cracked-machine/STM32MP1_TestBoard_RevB/STM32MP1_TestBoard_RevB/DDR.sch

## KiCad design STM32MP1_TestBoard_RevB/DDR.sch (2021-04-06)

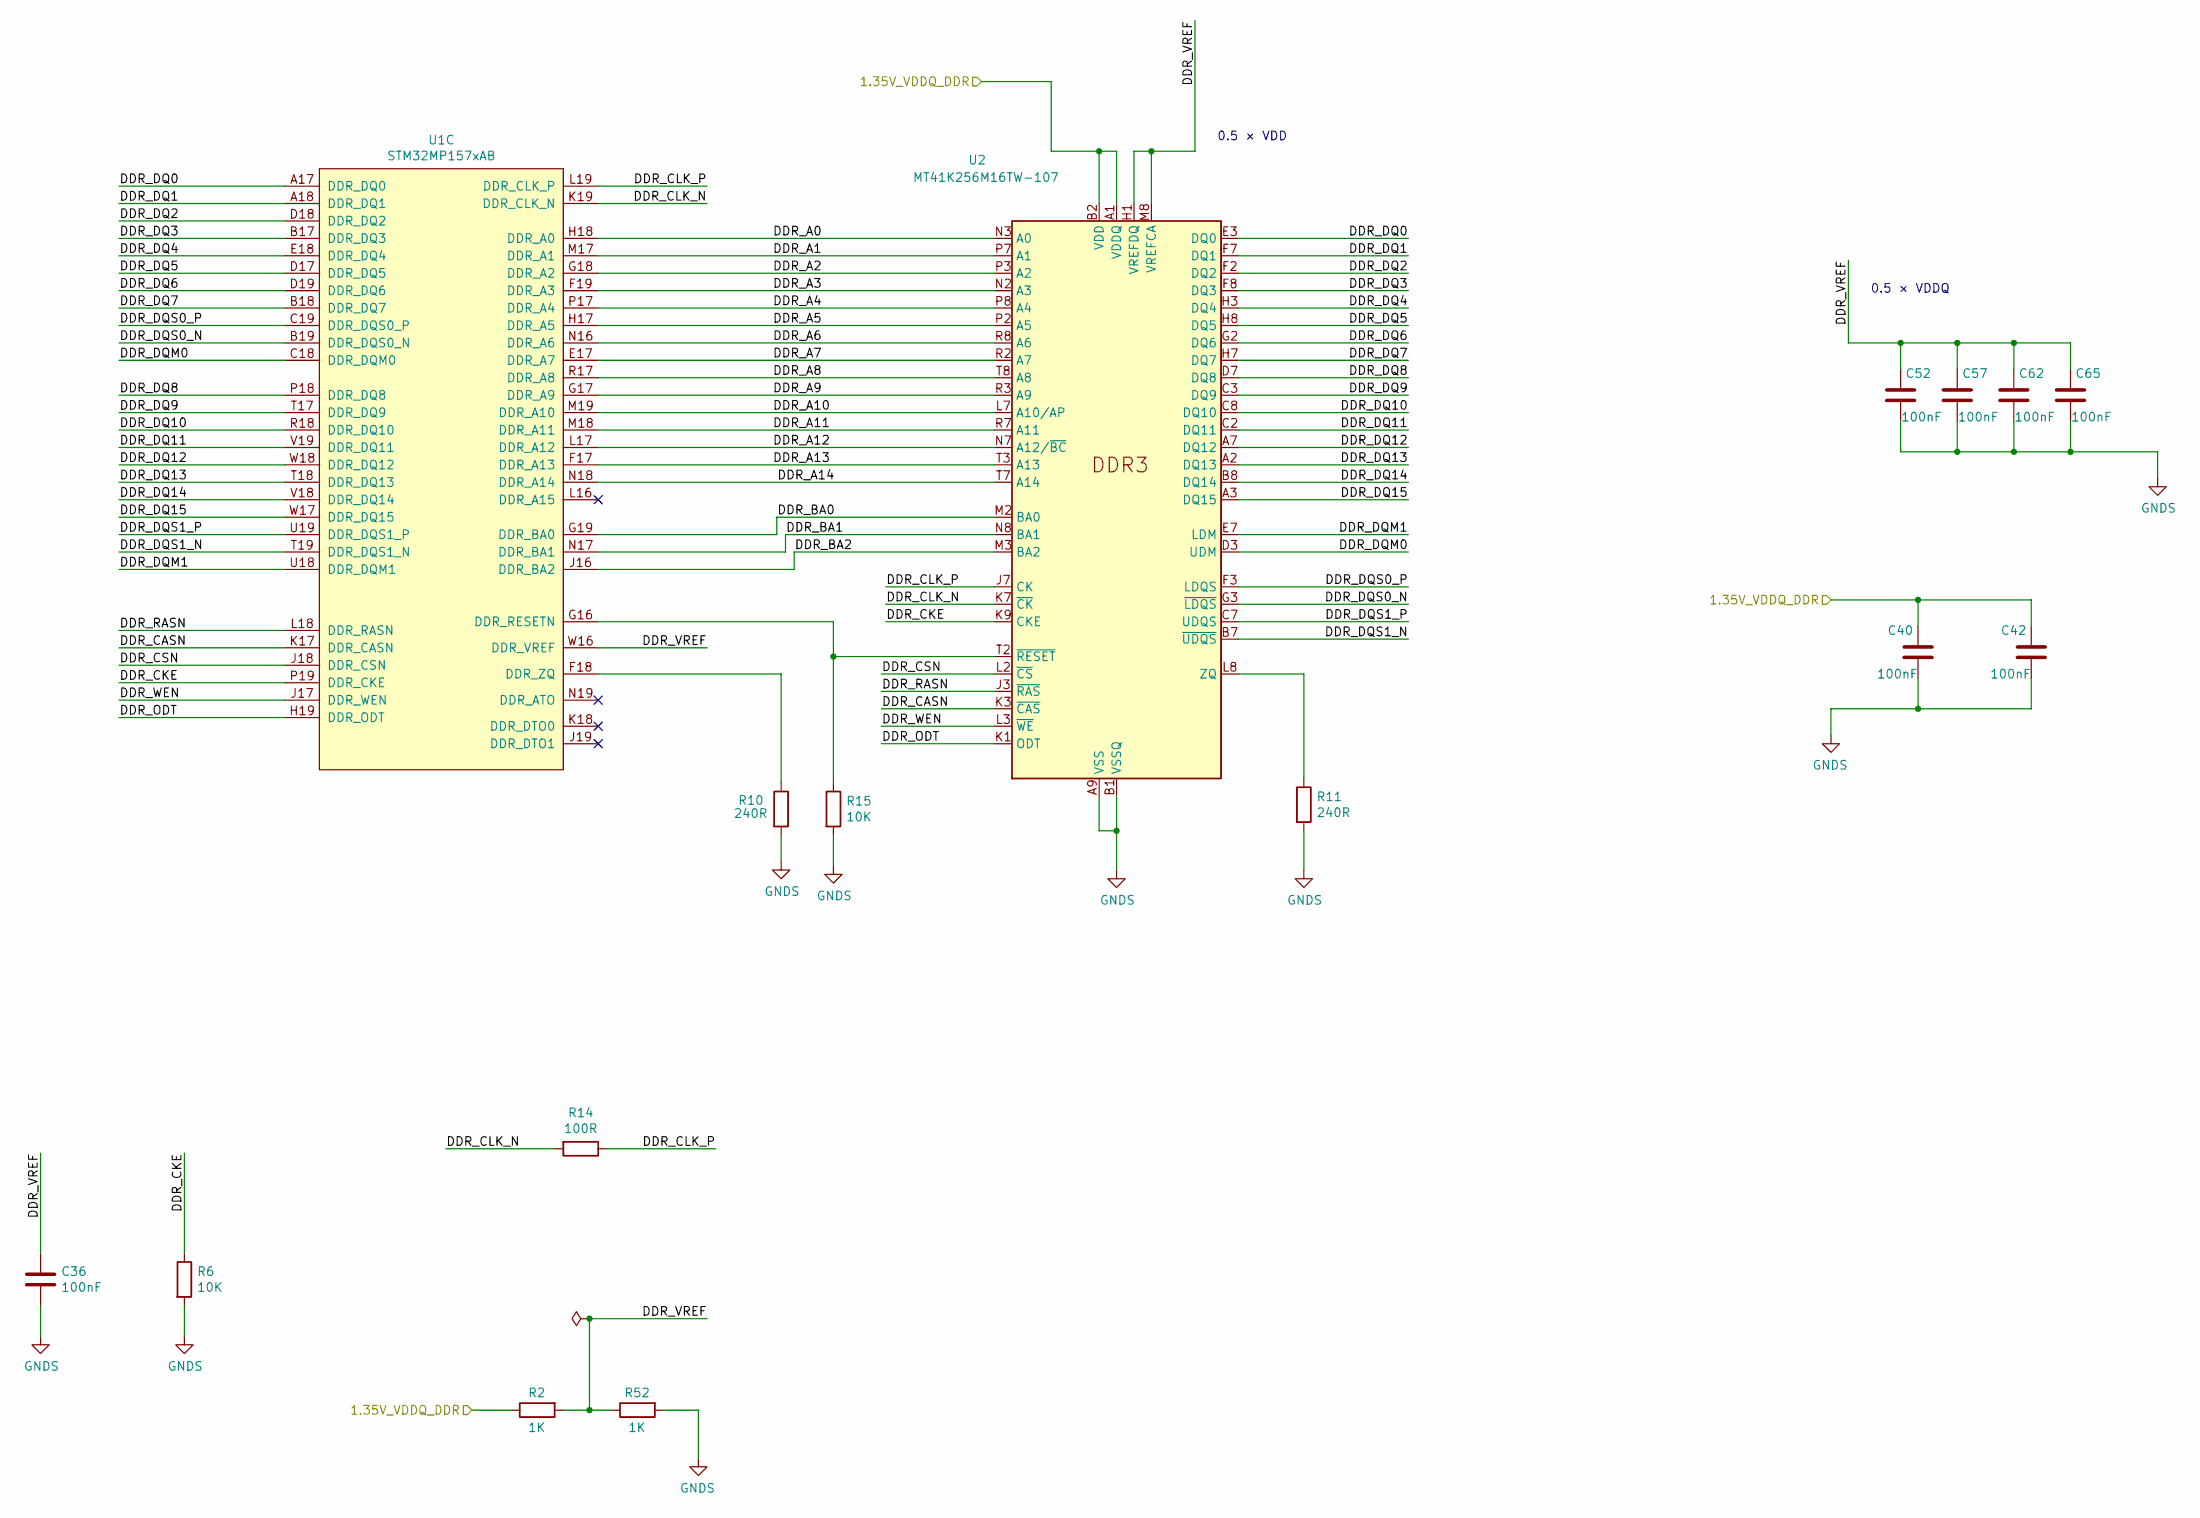
[picture p23: schematic DDR.sch]

Parts:
C36, C40, C42, C52, C57, C62, C65: 100nF; C_0402_1005Metric_Pad0.74x0.62mm_HandSolder; LCSC C1525
R2, R52: 1K; R_0402_1005Metric_Pad0.72x0.64mm_HandSolder; LCSC C11702
R6, R15: 10K; R_0402_1005Metric_Pad0.72x0.64mm_HandSolder; LCSC C25744
R10, R11: 240R; R_0402_1005Metric_Pad0.72x0.64mm_HandSolder
R14: 100R; R_0402_1005Metric_Pad0.72x0.64mm_HandSolder; LCSC C25076
U1: STM32MP157xAB; BGA-354_19x19_16.0x16.0mm
U2: MT41K256M16TW-107; BGA-96_9.0x13.0mm_Layout2x3x16_P0.8mm; PartNo MT41K256M16TW-107

Connections:
1.35V_VDDQ_DDR: C40.1, C42.1, R2.1, U2.A1 (VDDQ), U2.A8 (VDDQ), U2.B2 (VDD), U2.C1 (VDDQ), U2.C9 (VDDQ), U2.D2 (VDDQ), U2.D9 (VDD), U2.E9 (VDDQ), U2.F1 (VDDQ), U2.G7 (VDD), U2.H2 (VDDQ), U2.H9 (VDDQ), U2.K2 (VDD), U2.K8 (VDD), U2.N1 (VDD), U2.N9 (VDD), U2.R1 (VDD), U2.R9 (VDD)
DDR_A0: U1.H18 (DDR_A0), U2.N3 (A0)
DDR_A1: U1.M17 (DDR_A1), U2.P7 (A1)
DDR_A2: U1.G18 (DDR_A2), U2.P3 (A2)
DDR_A3: U1.F19 (DDR_A3), U2.N2 (A3)
DDR_A4: U1.P17 (DDR_A4), U2.P8 (A4)
DDR_A5: U1.H17 (DDR_A5), U2.P2 (A5)
DDR_A6: U1.N16 (DDR_A6), U2.R8 (A6)
DDR_A7: U1.E17 (DDR_A7), U2.R2 (A7)
DDR_A8: U1.R17 (DDR_A8), U2.T8 (A8)
DDR_A9: U1.G17 (DDR_A9), U2.R3 (A9)
DDR_A10: U1.M19 (DDR_A10), U2.L7 (A10/AP)
DDR_A11: U1.M18 (DDR_A11), U2.R7 (A11)
DDR_A12: U1.L17 (DDR_A12), U2.N7 (A12/~BC)
DDR_A13: U1.F17 (DDR_A13), U2.T3 (A13)
DDR_A14: U1.N18 (DDR_A14), U2.T7 (A14)
DDR_BA0: U1.G19 (DDR_BA0), U2.M2 (BA0)
DDR_BA1: U1.N17 (DDR_BA1), U2.N8 (BA1)
DDR_BA2: U1.J16 (DDR_BA2), U2.M3 (BA2)
DDR_CASN: U1.K17 (DDR_CASN), U2.K3 (~CAS)
DDR_CKE: R6.1, U1.P19 (DDR_CKE), U2.K9 (CKE)
DDR_CLK_N: R14.2, U1.K19 (DDR_CLK_N), U2.K7 (~CK)
DDR_CLK_P: R14.1, U1.L19 (DDR_CLK_P), U2.J7 (CK)
DDR_CSN: U1.J18 (DDR_CSN), U2.L2 (~CS)
DDR_DQ0: U1.A17 (DDR_DQ0), U2.E3 (DQ0)
DDR_DQ1: U1.A18 (DDR_DQ1), U2.F7 (DQ1)
DDR_DQ2: U1.D18 (DDR_DQ2), U2.F2 (DQ2)
DDR_DQ3: U1.B17 (DDR_DQ3), U2.F8 (DQ3)
DDR_DQ4: U1.E18 (DDR_DQ4), U2.H3 (DQ4)
DDR_DQ5: U1.D17 (DDR_DQ5), U2.H8 (DQ5)
DDR_DQ6: U1.D19 (DDR_DQ6), U2.G2 (DQ6)
DDR_DQ7: U1.B18 (DDR_DQ7), U2.H7 (DQ7)
DDR_DQ8: U1.P18 (DDR_DQ8), U2.D7 (DQ8)
DDR_DQ9: U1.T17 (DDR_DQ9), U2.C3 (DQ9)
DDR_DQ10: U1.R18 (DDR_DQ10), U2.C8 (DQ10)
DDR_DQ11: U1.V19 (DDR_DQ11), U2.C2 (DQ11)
DDR_DQ12: U1.W18 (DDR_DQ12), U2.A7 (DQ12)
DDR_DQ13: U1.T18 (DDR_DQ13), U2.A2 (DQ13)
DDR_DQ14: U1.V18 (DDR_DQ14), U2.B8 (DQ14)
DDR_DQ15: U1.W17 (DDR_DQ15), U2.A3 (DQ15)
DDR_DQM0: U1.C18 (DDR_DQM0), U2.D3 (UDM)
DDR_DQM1: U1.U18 (DDR_DQM1), U2.E7 (LDM)
DDR_DQS0_N: U1.B19 (DDR_DQS0_N), U2.G3 (~LDQS)
DDR_DQS0_P: U1.C19 (DDR_DQS0_P), U2.F3 (LDQS)
DDR_DQS1_N: U1.T19 (DDR_DQS1_N), U2.B7 (~UDQS)
DDR_DQS1_P: U1.U19 (DDR_DQS1_P), U2.C7 (UDQS)
DDR_ODT: U1.H19 (DDR_ODT), U2.K1 (ODT)
DDR_RASN: U1.L18 (DDR_RASN), U2.J3 (~RAS)
DDR_VREF: C36.1, C52.1, C57.1, C62.1, C65.1, R2.2, R52.1, U1.W16 (DDR_VREF), U2.H1 (VREFDQ), U2.M8 (VREFCA)
DDR_WEN: U1.J17 (DDR_WEN), U2.L3 (~WE)
GNDS: C36.2, C40.2, C42.2, C52.2, C57.2, C62.2, C65.2, R6.2, R10.2, R11.2, R15.2, R52.2, U2.A9 (VSS), U2.B1 (VSSQ), U2.B3 (VSS), U2.B9 (VSSQ), U2.D1 (VSSQ), U2.D8 (VSSQ), U2.E1 (VSS), U2.E2 (VSSQ), U2.E8 (VSSQ), U2.F9 (VSSQ), U2.G1 (VSSQ), U2.G8 (VSS), U2.G9 (VSSQ), U2.J2 (VSS), U2.J8 (VSS), U2.M1 (VSS), U2.M9 (VSS), U2.P1 (VSS), U2.P9 (VSS), U2.T1 (VSS), U2.T9 (VSS)
unnamed: R10.1, U1.F18 (DDR_ZQ)
unnamed: R11.1, U2.L8 (ZQ)
unnamed: R15.1, U1.G16 (DDR_RESETN), U2.T2 (~RESET)

Notes on the sheet:
0.5 × VDDQ
0.5 × VDD
