cracked-machine/STM32MP1_TestBoard_RevB/STM32MP1_TestBoard_RevB/DebugInterface.sch

## KiCad design STM32MP1_TestBoard_RevB/DebugInterface.sch (2021-04-06)

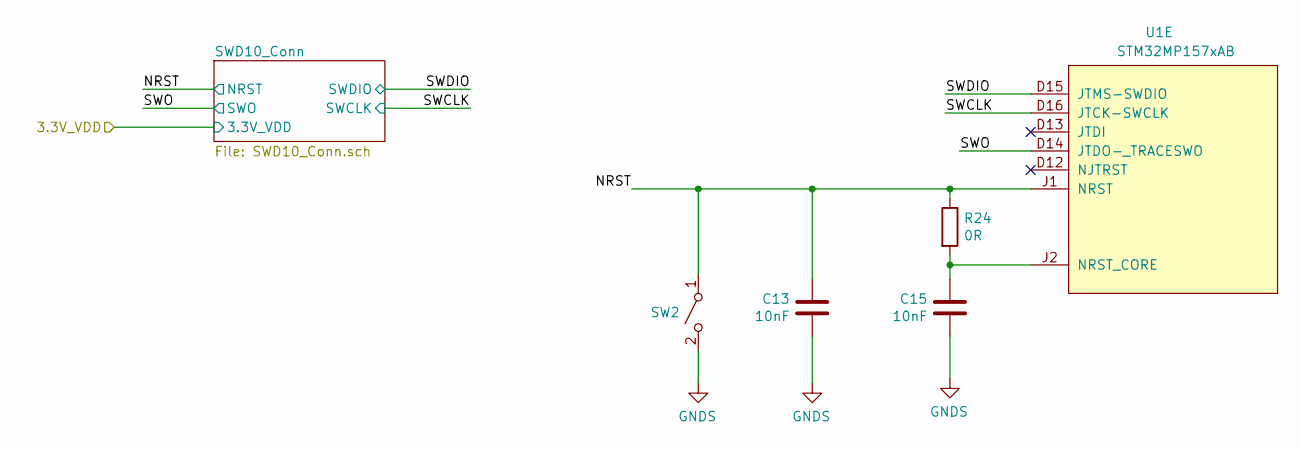
[picture p24: schematic DebugInterface.sch]

Parts:
C13, C15: 10nF; C_0402_1005Metric_Pad0.74x0.62mm_HandSolder; LCSC C15195
R24: 0R; R_0402_1005Metric_Pad0.72x0.64mm_HandSolder; LCSC C25087
SW2: SW_SPST; Panasonic_EVQPUK_EVQPUB
U1: STM32MP157xAB; BGA-354_19x19_16.0x16.0mm

Connections:
GNDS: C13.2, C15.2, SW2.2 (B)
NRST: C13.1, R24.1, SW2.1 (A), U1.J1 (NRST)
unnamed: C15.1, R24.2, U1.J2 (NRST_CORE)
SWCLK: U1.D16 (JTCK-SWCLK)
SWDIO: U1.D15 (JTMS-SWDIO)
SWO: U1.D14 (JTDO-_TRACESWO)
