cracked-machine/STM32MP1_TestBoard_RevB/STM32MP1_TestBoard_RevB/GPIO.sch

## KiCad design STM32MP1_TestBoard_RevB/GPIO.sch (2021-06-18)

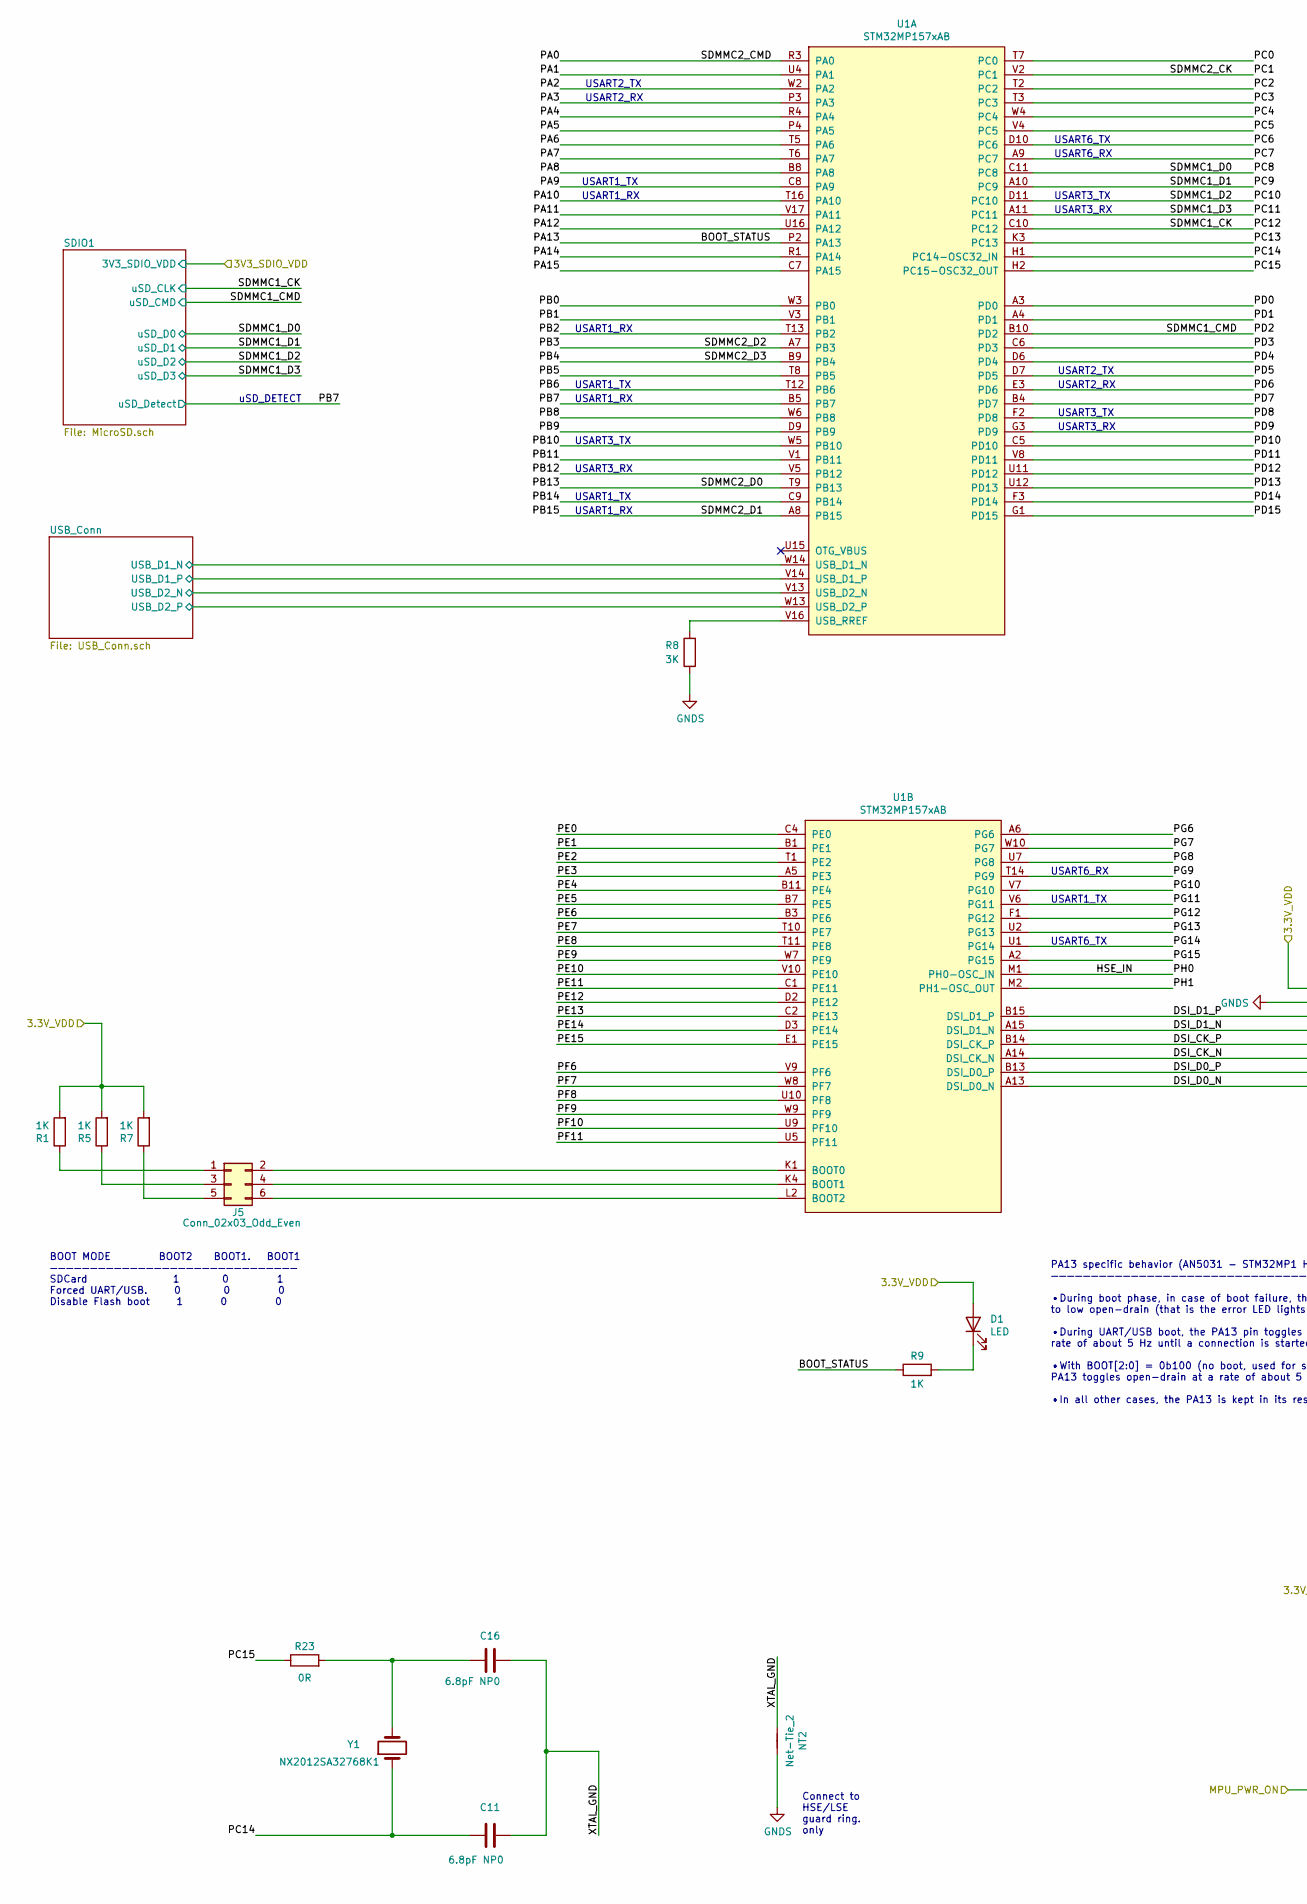
[picture p25: schematic GPIO.sch, part in row 1, column 1]

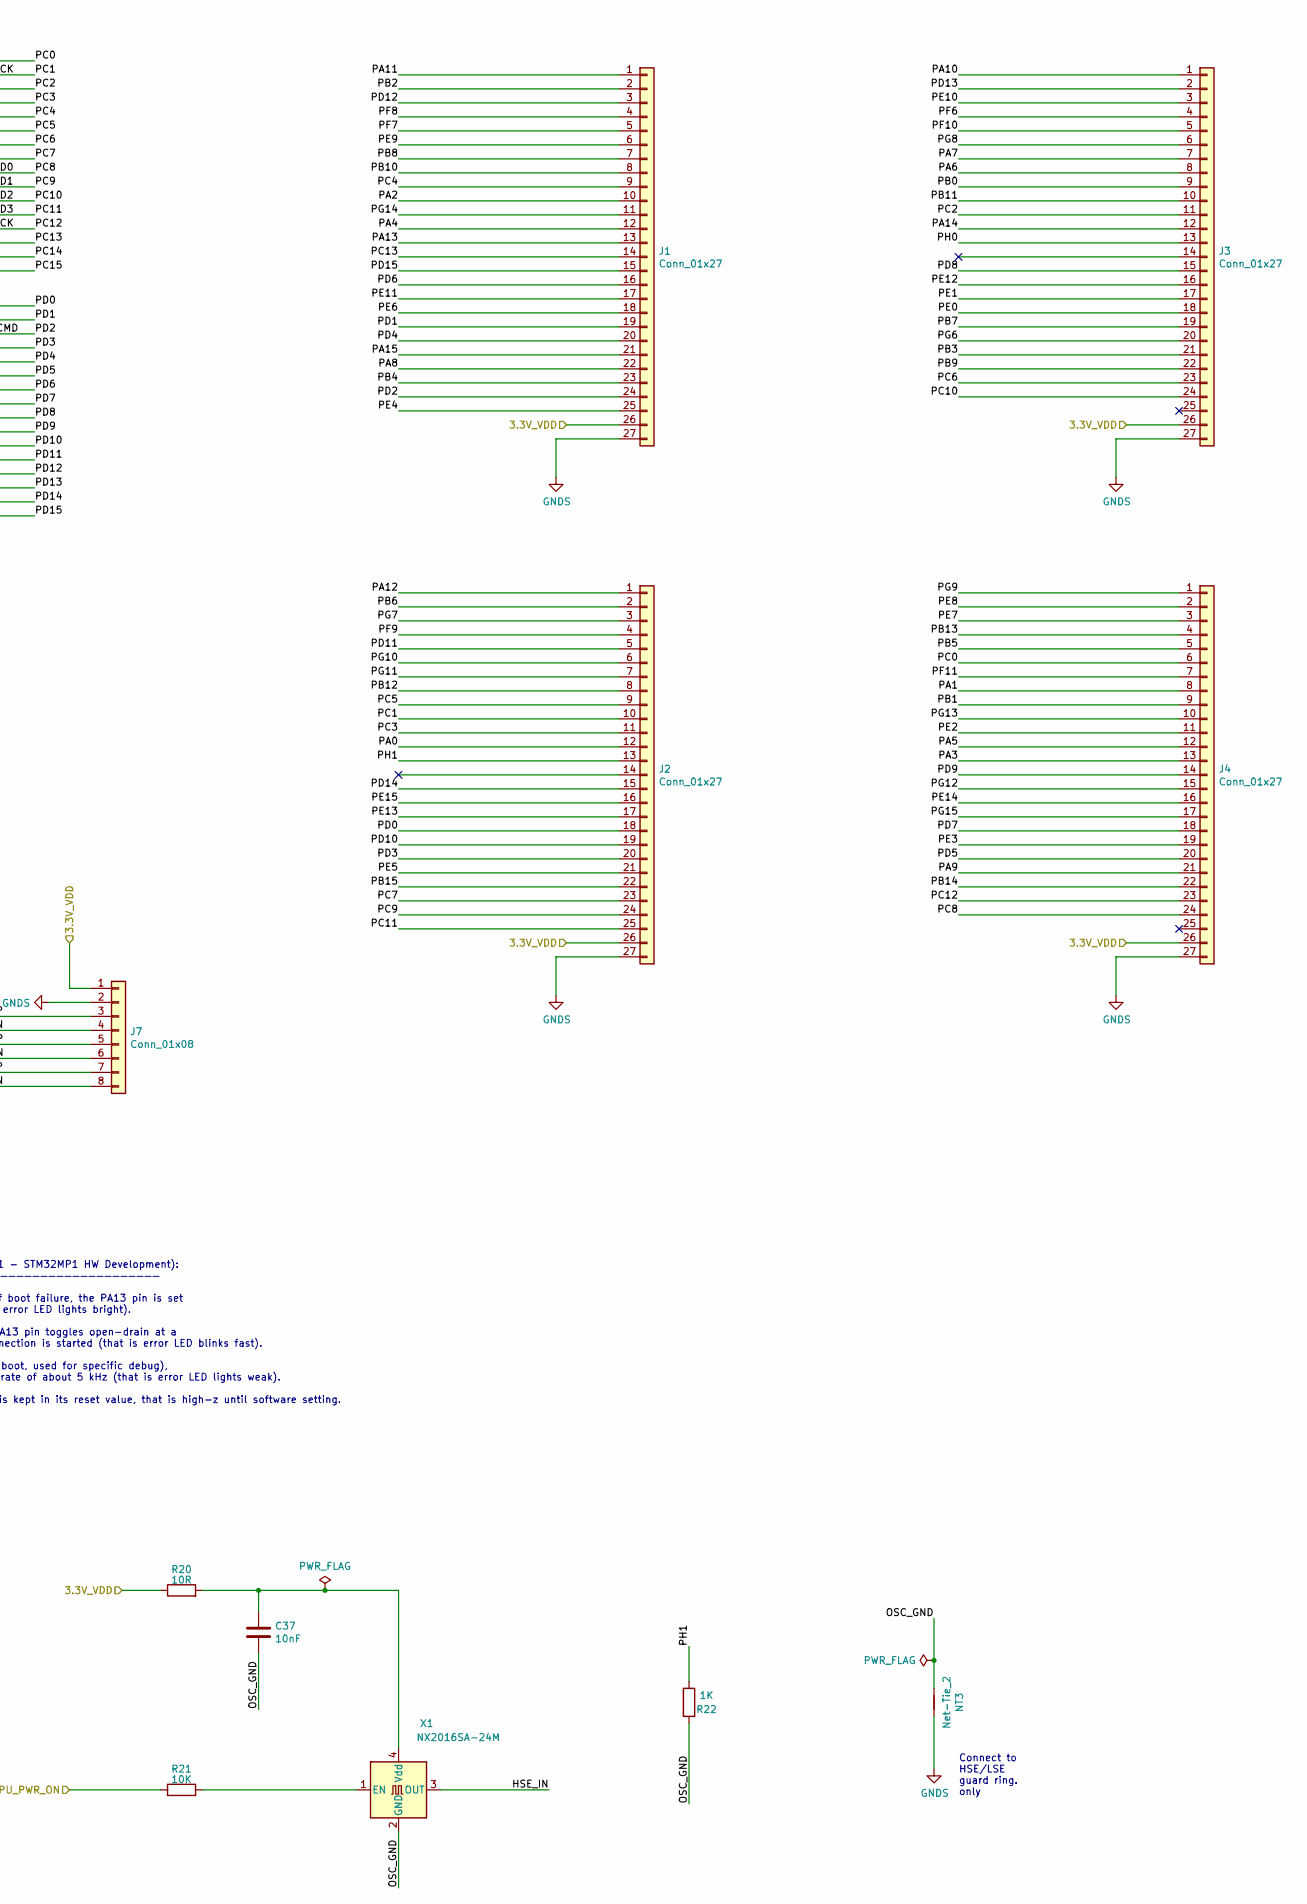
[picture p26: schematic GPIO.sch, part in row 1, column 2]

Parts:
C11, C16: 6.8pF NP0; C_0402_1005Metric_Pad0.74x0.62mm_HandSolder; LCSC C1576
C37: 10nF; C_0402_1005Metric_Pad0.74x0.62mm_HandSolder; LCSC C15195
D1: LED; LED_0805_2012Metric_Pad1.15x1.40mm_HandSolder; LCSC C84256
J1, J2, J3, J4: Conn_01x27; PinHeader_1x27_P2.54mm_Vertical
J5: Conn_02x03_Odd_Even; PinHeader_2x03_P2.54mm_Vertical
J7: Conn_01x08; PinHeader_1x08_P2.54mm_Vertical
NT2, NT3: Net-Tie_2; NetTie-2_SMD_Pad0.127mm
R1, R5, R7, R9, R22: 1K; R_0402_1005Metric_Pad0.72x0.64mm_HandSolder; LCSC C11702
R8: 3K; R_0402_1005Metric_Pad0.72x0.64mm_HandSolder
R20: 10R; R_0402_1005Metric_Pad0.72x0.64mm_HandSolder; LCSC C25077
R21: 10K; R_0402_1005Metric_Pad0.72x0.64mm_HandSolder; LCSC C25744
R23: 0R; R_0402_1005Metric_Pad0.72x0.64mm_HandSolder; LCSC C25087
U1: STM32MP157xAB; BGA-354_19x19_16.0x16.0mm
X1: NX2016SA-24M; Oscillator_SMD_Abracon_ASE-4Pin_3.2x2.5mm; PartNo NX2016SA-24M-EXS00A-CS08891; Mouser 344-NX2016SA24S08891
Y1: NX2012SA32768K1; Crystal_SMD_2012-2Pin_2.0x1.2mm_HandSoldering; PartNo ECS-.327-12.5-12R-TR; Mouser 520-.327-12.5-12R-T

Connections:
3.3V_VDD: D1.2 (A), J1.26, J2.26, J3.26, J4.26, J7.1, R1.2, R5.2, R7.2, R20.1
BOOT_STATUS: J1.13, R9.1, U1.P2 (PA13)
DSI_CK_N: J7.6, U1.A14 (DSI_CK_N)
DSI_CK_P: J7.5, U1.B14 (DSI_CK_P)
DSI_D0_N: J7.8, U1.A13 (DSI_D0_N)
DSI_D0_P: J7.7, U1.B13 (DSI_D0_P)
DSI_D1_N: J7.4, U1.A15 (DSI_D1_N)
DSI_D1_P: J7.3, U1.B15 (DSI_D1_P)
GNDS: J1.27, J2.27, J3.27, J4.27, J7.2, NT2.1, NT3.1, R8.1
HSE_IN: J3.13, U1.M1 (PH0-OSC_IN), X1.3 (OUT)
MPU_PWR_ON: R21.1
unnamed: C16.2, R23.2, Y1.2
unnamed: C37.2, R20.2, X1.4 (Vdd)
unnamed: D1.1 (K), R9.2
unnamed: J5.1, R1.1
unnamed: J5.2, U1.K1 (BOOT0)
unnamed: J5.3, R5.1
unnamed: J5.4, U1.K4 (BOOT1)
unnamed: J5.5, R7.1
unnamed: J5.6, U1.L2 (BOOT2)
unnamed: R8.2, U1.V16 (USB_RREF)
unnamed: R21.2, X1.1 (EN)
OSC_GND: C37.1, NT3.2, R22.2, X1.2 (GND)
PA0: J2.12, U1.R3 (PA0)
PA1: J4.8, U1.U4 (PA1)
PA2: J1.10, U1.W2 (PA2)
PA3: J4.13, U1.P3 (PA3)
PA4: J1.12, U1.R4 (PA4)
PA5: J4.12, U1.P4 (PA5)
PA6: J3.8, U1.T5 (PA6)
PA7: J3.7, U1.T6 (PA7)
PA8: J1.22, U1.B8 (PA8)
PA9: J4.21, U1.C8 (PA9)
PA10: J3.1, U1.T16 (PA10)
PA11: J1.1, U1.V17 (PA11)
PA12: J2.1, U1.U16 (PA12)
PA14: J3.12, U1.R1 (PA14)
PA15: J1.21, U1.C7 (PA15)
PB0: J3.9, U1.W3 (PB0)
PB1: J4.9, U1.V3 (PB1)
PB2: J1.2, U1.T13 (PB2)
PB3: J3.21, U1.A7 (PB3)
PB4: J1.23, U1.B9 (PB4)
PB5: J4.5, U1.T8 (PB5)
PB6: J2.2, U1.T12 (PB6)
PB7: J3.19, U1.B5 (PB7)
PB8: J1.7, U1.W6 (PB8)
PB9: J3.22, U1.D9 (PB9)
PB10: J1.8, U1.W5 (PB10)
PB11: J3.10, U1.V1 (PB11)
PB12: J2.8, U1.V5 (PB12)
PB13: J4.4, U1.T9 (PB13)
PB14: J4.22, U1.C9 (PB14)
PB15: J2.22, U1.A8 (PB15)
PC0: J4.6, U1.T7 (PC0)
PC1: J2.10, U1.V2 (PC1)
PC2: J3.11, U1.T2 (PC2)
PC3: J2.11, U1.T3 (PC3)
PC4: J1.9, U1.W4 (PC4)
PC5: J2.9, U1.V4 (PC5)
PC6: J3.23, U1.D10 (PC6)
PC7: J2.23, U1.A9 (PC7)
PC8: J4.24, U1.C11 (PC8)
PC9: J2.24, U1.A10 (PC9)
PC10: J3.24, U1.D11 (PC10)
PC11: J2.25, U1.A11 (PC11)
PC12: J4.23, U1.C10 (PC12)
PC13: J1.14, U1.K3 (PC13)
PC14: C11.2, U1.H1 (PC14-OSC32_IN), Y1.1
PC15: R23.1, U1.H2 (PC15-OSC32_OUT)
PD0: J2.18, U1.A3 (PD0)
PD1: J1.19, U1.A4 (PD1)
PD2: J1.24, U1.B10 (PD2)
PD3: J2.20, U1.C6 (PD3)
PD4: J1.20, U1.D6 (PD4)
PD5: J4.20, U1.D7 (PD5)
PD6: J1.16, U1.E3 (PD6)
PD7: J4.18, U1.B4 (PD7)
PD8: J3.15, U1.F2 (PD8)
PD9: J4.14, U1.G3 (PD9)
PD10: J2.19, U1.C5 (PD10)
PD11: J2.5, U1.V8 (PD11)
PD12: J1.3, U1.U11 (PD12)
PD13: J3.2, U1.U12 (PD13)
PD14: J2.15, U1.F3 (PD14)
PD15: J1.15, U1.G1 (PD15)
PE0: J3.18, U1.C4 (PE0)
PE1: J3.17, U1.B1 (PE1)
PE2: J4.11, U1.T1 (PE2)
PE3: J4.19, U1.A5 (PE3)
PE4: J1.25, U1.B11 (PE4)
PE5: J2.21, U1.B7 (PE5)
PE6: J1.18, U1.B3 (PE6)
PE7: J4.3, U1.T10 (PE7)
PE8: J4.2, U1.T11 (PE8)
PE9: J1.6, U1.W7 (PE9)
PE10: J3.3, U1.V10 (PE10)
PE11: J1.17, U1.C1 (PE11)
PE12: J3.16, U1.D2 (PE12)
PE13: J2.17, U1.C2 (PE13)
PE14: J4.16, U1.D3 (PE14)
PE15: J2.16, U1.E1 (PE15)
PF6: J3.4, U1.V9 (PF6)
PF7: J1.5, U1.W8 (PF7)
PF8: J1.4, U1.U10 (PF8)
PF9: J2.4, U1.W9 (PF9)
PF10: J3.5, U1.U9 (PF10)
PF11: J4.7, U1.U5 (PF11)
PG6: J3.20, U1.A6 (PG6)
PG7: J2.3, U1.W10 (PG7)
PG8: J3.6, U1.U7 (PG8)
PG9: J4.1, U1.T14 (PG9)
PG10: J2.6, U1.V7 (PG10)
PG11: J2.7, U1.V6 (PG11)
PG12: J4.15, U1.F1 (PG12)
PG13: J4.10, U1.U2 (PG13)
PG14: J1.11, U1.U1 (PG14)
PG15: J4.17, U1.A2 (PG15)
PH1: J2.13, R22.1, U1.M2 (PH1-OSC_OUT)
USB_D1_N: U1.W14 (USB_D1_N)
USB_D1_P: U1.V14 (USB_D1_P)
USB_D2_N: U1.V13 (USB_D2_N)
USB_D2_P: U1.W13 (USB_D2_P)
XTAL_GND: C11.1, C16.1, NT2.2

Notes on the sheet:
BOOT MODE BOOT2 BOOT1. BOOT1 ——————————————————————————————— SDCard 1 0 1 Forced UART/USB. 0 0 0 Disable Flash boot 1 0 0
USART2_RX
USART3_TX
USART3_RX
USART6_TX
USART2_TX
USART1_TX
USART1_RX
USART6_RX
uSD_DETECT
Connect to HSE/LSE guard ring. only
PA13 specific behavior (AN5031 - STM32MP1 HW Development): ————————————————————————————————————————— •During boot phase, in case of boot failure, the PA13 pin is set to low open-drain (that is the error LED lights bright). •During UART/USB boot, the PA13 pin toggles open-drain at a rate of about 5 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
