cracked-machine/STM32MP1_TestBoard_RevB/STM32MP1_TestBoard_RevB/MicroSD.sch

## KiCad design STM32MP1_TestBoard_RevB/MicroSD.sch (2021-04-06)

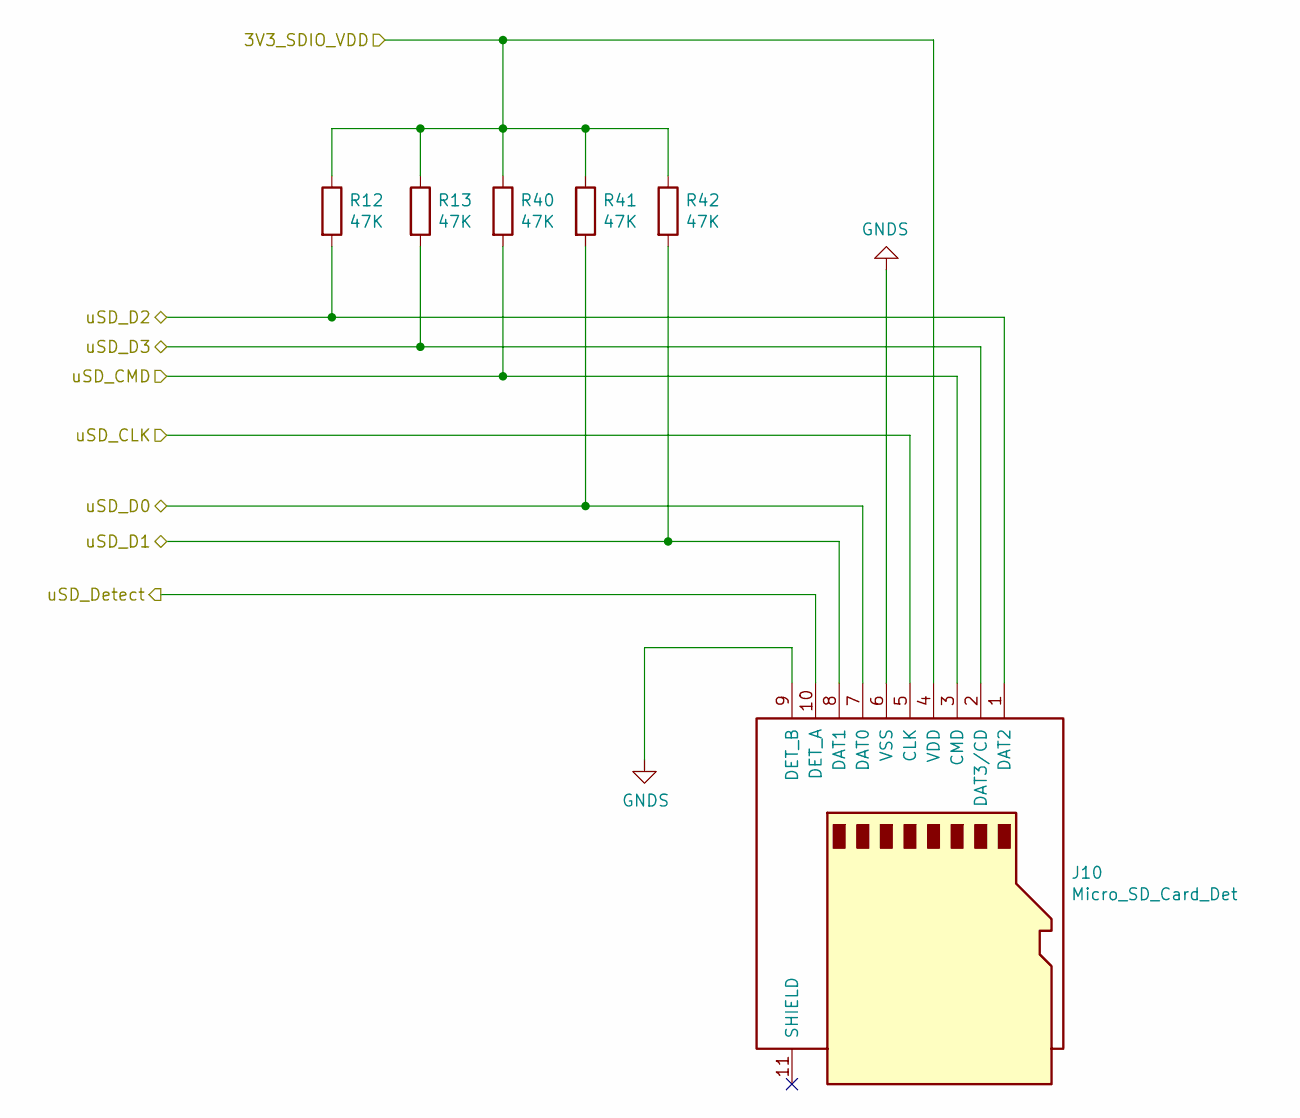
[picture p27: schematic MicroSD.sch]

Parts:
J10: Micro_SD_Card_Det; microSD_HC_Molex_104031-0811; PartNo 104031-0811; Mouser 538-104031-0811
R40, R41, R42, R43, R44: 47K; R_0402_1005Metric_Pad0.72x0.64mm_HandSolder; LCSC C25792

Connections:
3V3_SDIO_VDD: J10.4 (VDD), R40.1, R41.1, R42.1, R43.1, R44.1
GNDS: J10.6 (VSS), J10.9 (DET_B)
uSD_CLK: J10.5 (CLK)
uSD_CMD: J10.3 (CMD), R42.2
uSD_D0: J10.7 (DAT0), R43.2
uSD_D1: J10.8 (DAT1), R44.2
uSD_D2: J10.1 (DAT2), R40.2
uSD_D3: J10.2 (DAT3/CD), R41.2
uSD_Detect: J10.10 (DET_A)
