cracked-machine/STM32MP1_TestBoard_RevB/STM32MP1_TestBoard_RevB/PSU.sch

## KiCad design STM32MP1_TestBoard_RevB/PSU.sch (2021-06-18)

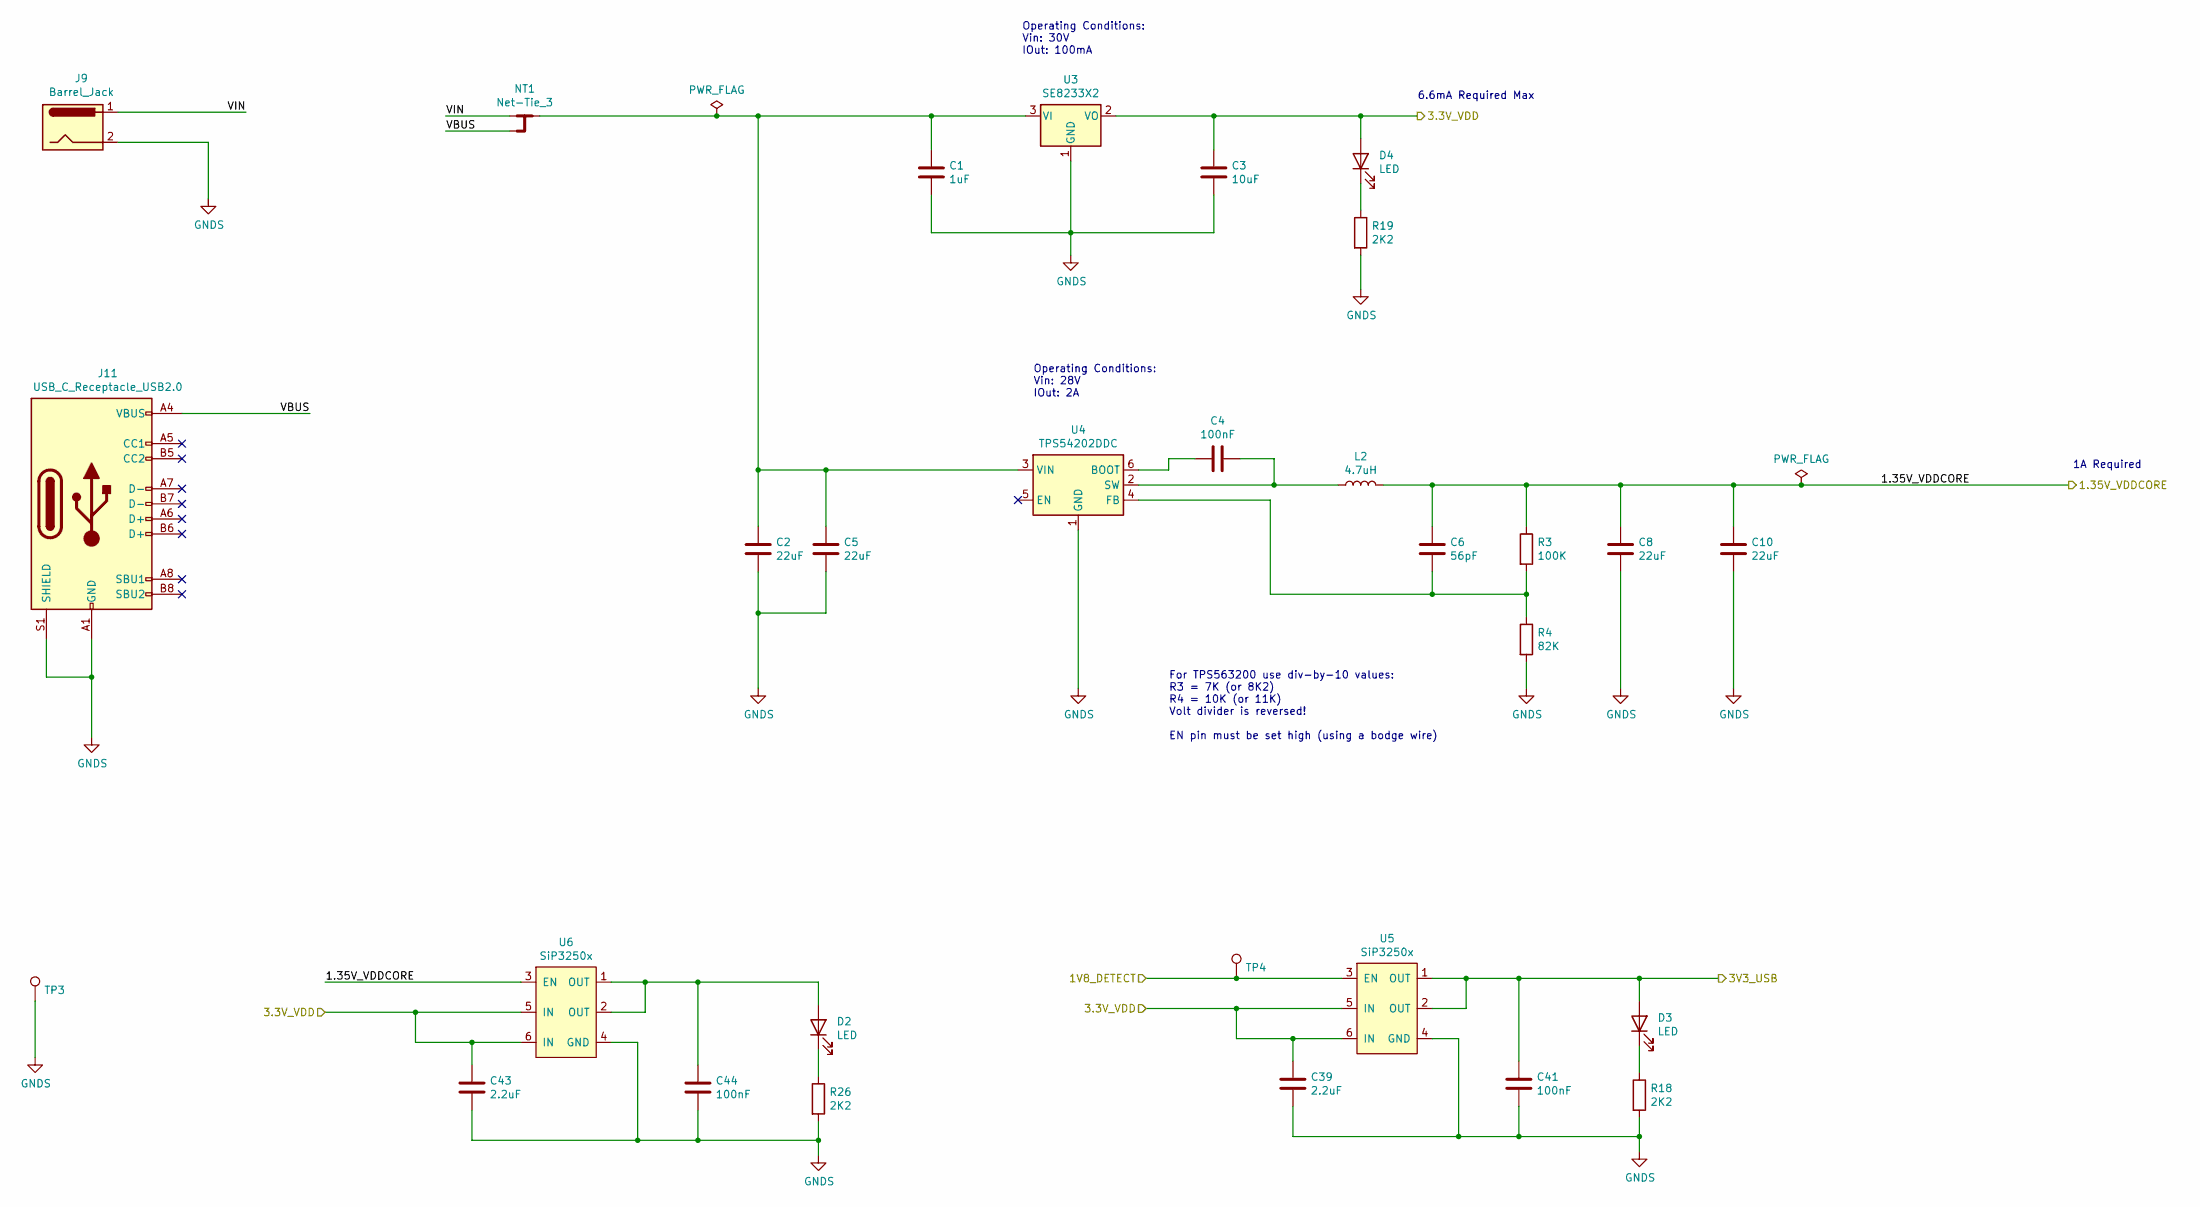
[picture p28: schematic PSU.sch]

Parts:
C1: 1uF; C_0402_1005Metric_Pad0.74x0.62mm_HandSolder; LCSC C52923
C2, C5, C8, C10: 22uF; C_1206_3216Metric_Pad1.33x1.80mm_HandSolder; PartNo C1206C226M8PACTU
C3: 10uF; C_0402_1005Metric_Pad0.74x0.62mm_HandSolder; LCSC C15525
C4, C41, C44: 100nF; C_0402_1005Metric_Pad0.74x0.62mm_HandSolder; LCSC C1525
C6: 56pF; C_0402_1005Metric_Pad0.74x0.62mm_HandSolder; LCSC C1572
C39, C43: 2.2uF; C_0603_1608Metric_Pad1.08x0.95mm_HandSolder; LCSC C23630
D2, D3, D4: LED; LED_0805_2012Metric_Pad1.15x1.40mm_HandSolder; LCSC C84256
J9: Barrel_Jack; BarrelJack_Horizontal
J11: USB_C_Receptacle_USB2.0; 213716-0001_THT_Socket_RightAngle; PartNo 213716-0001; Mouser 538-213716-0001
L2: 4.7uH; L_Bourns-SRN6028; PartNo SMNR6028-4R7MT
NT1: Net-Tie_3; NetTie-3_SMD_Pad0.5mm
R3: 100K; R_0402_1005Metric_Pad0.72x0.64mm_HandSolder; LCSC C25741
R4: 82K; R_0402_1005Metric_Pad0.72x0.64mm_HandSolder; LCSC C25571
R18, R19, R26: 2K2; R_0402_1005Metric_Pad0.72x0.64mm_HandSolder; LCSC C25879
TP3, TP4: TestPoint; TestPoint_Pad_D1.0mm
U3: SE8233X2; SOT-23
U4: TPS54202DDC; SOT-23-6; PartNo TPS54202DDCR
U5, U6: SiP3250x; SOT-23-6_Handsoldering; PartNo SIP32508DT-T1-GE3; Mouser 78-SIP32508DT-T1-GE3

Connections:
1.35V_VDDCORE: C6.2, C8.1, C10.1, L2.2, R3.1, U6.3 (EN)
1V8_DETECT: TP4.1, U5.3 (EN)
3.3V_VDD: C3.1, C39.1, C43.1, D4.2 (A), U3.2 (VO), U5.5 (IN), U5.6 (IN), U6.5 (IN), U6.6 (IN)
3V3_USB: C41.1, D3.2 (A), U5.1 (OUT), U5.2 (OUT)
GNDS: C1.2, C2.2, C3.2, C5.2, C8.2, C10.2, C39.2, C41.2, C43.2, C44.2, J9.2, J11.A1 (GND), J11.A12 (GND), J11.B1 (GND), J11.B12 (GND), J11.S1 (SHIELD), R4.2, R18.2, R19.2, R26.2, TP3.1, U3.1 (GND), U4.1 (GND), U5.4 (GND), U6.4 (GND)
unnamed: C1.1, C2.1, C5.1, NT1.2, U3.3 (VI), U4.3 (VIN)
unnamed: C4.1, L2.1, U4.2 (SW)
unnamed: C4.2, U4.6 (BOOT)
unnamed: C6.1, R3.2, R4.1, U4.4 (FB)
unnamed: C44.1, D2.2 (A), U6.1 (OUT), U6.2 (OUT)
unnamed: D2.1 (K), R26.1
unnamed: D3.1 (K), R18.1
unnamed: D4.1 (K), R19.1
VBUS: J11.A4 (VBUS), J11.A9 (VBUS), J11.B4 (VBUS), J11.B9 (VBUS), NT1.3
VIN: J9.1, NT1.1

Notes on the sheet:
6.6mA Required Max
1A Required
Operating Conditions: Vin: 30V IOut: 100mA
Operating Conditions: Vin: 28V IOut: 2A
For TPS563200 use div-by-10 values: R3 = 7K (or 8K2) R4 = 10K (or 11K) Volt divider is reversed! EN pin must be set high (using a bodge wire)
