cracked-machine/STM32MP1_TestBoard_RevB/STM32MP1_TestBoard_RevB/Power_MPU.sch

## KiCad design STM32MP1_TestBoard_RevB/Power_MPU.sch (2021-04-06)

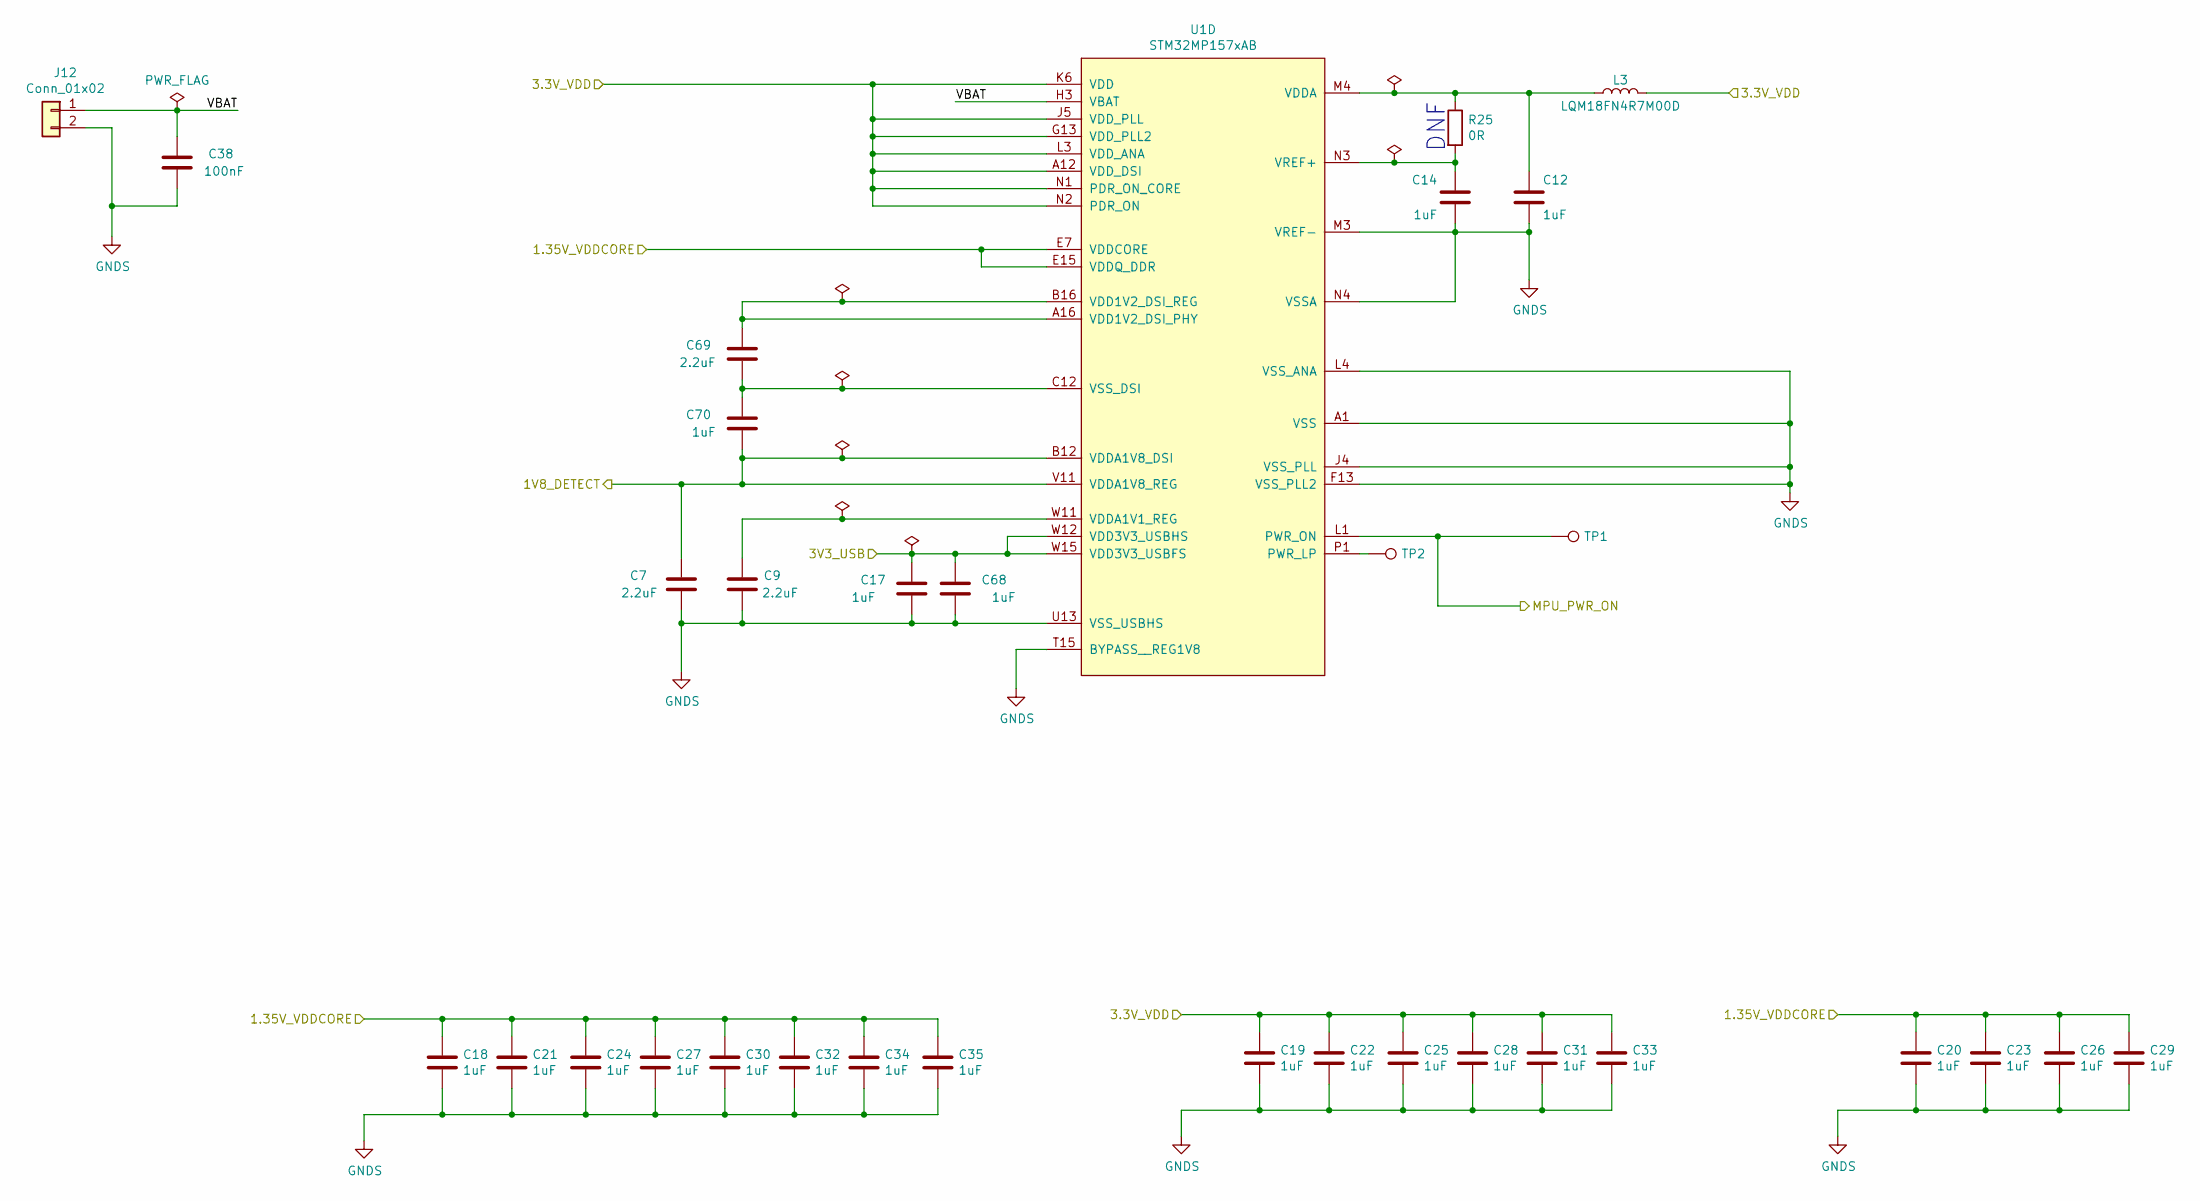
[picture p29: schematic Power_MPU.sch]

Parts:
C7, C9, C69: 2.2uF; C_0402_1005Metric_Pad0.74x0.62mm_HandSolder; PartNo LMK105BJ105KV-F
C12, C14, C17, C18, C19, C20, C21, C22, C23, C24, C25, C26, C27, C28, C29, C30, C31, C32, C33, C34, C35, C68, C70: 1uF; C_0402_1005Metric_Pad0.74x0.62mm_HandSolder; PartNo LMK105BJ105KV-F; LCSC C52923
C38: 100nF; C_0402_1005Metric_Pad0.74x0.62mm_HandSolder; LCSC C1525
J12: Conn_01x02; Molex_KK-254_AE-6410-02A_1x02_P2.54mm_Vertical
L3: LQM18FN4R7M00D; L_0201_0603Metric_Pad0.64x0.40mm_HandSolder; Mouser 81-LQM18FN4R7M00D
R25: 0R; C_0402_1005Metric_Pad0.74x0.62mm_HandSolder; LCSC C25087
TP1, TP2: TestPoint; TestPoint_Pad_D1.0mm
U1: STM32MP157xAB; BGA-354_19x19_16.0x16.0mm

Connections:
1.35V_VDDCORE: C18.1, C20.1, C21.1, C23.1, C24.1, C26.1, C27.1, C29.1, C30.1, C32.1, C34.1, C35.1, U1.E7 (VDDCORE), U1.E9 (VDDCORE), U1.E11 (VDDCORE), U1.E13 (VDDCORE), U1.E15 (VDDQ_DDR), U1.F4 (VDDCORE), U1.F6 (VDDCORE), U1.F8 (VDDCORE), U1.F10 (VDDCORE), U1.F12 (VDDCORE), U1.F14 (VDDQ_DDR), U1.G5 (VDDCORE), U1.G7 (VDDCORE), U1.G9 (VDDCORE), U1.G11 (VDDCORE), U1.G15 (VDDQ_DDR), U1.H4 (VDDCORE), U1.H6 (VDDCORE), U1.H8 (VDDCORE), U1.H10 (VDDCORE), U1.H12 (VDDCORE), U1.H14 (VDDQ_DDR), U1.J7 (VDDCORE), U1.J9 (VDDCORE), U1.J11 (VDDCORE), U1.J13 (VDDCORE), U1.J15 (VDDQ_DDR), U1.K8 (VDDCORE), U1.K10 (VDDCORE), U1.K12 (VDDCORE), U1.K14 (VDDQ_DDR), U1.L9 (VDDCORE), U1.L11 (VDDCORE), U1.L13 (VDDCORE), U1.L15 (VDDQ_DDR), U1.M10 (VDDCORE), U1.M12 (VDDCORE), U1.M14 (VDDQ_DDR), U1.N11 (VDDCORE), U1.N13 (VDDCORE), U1.N15 (VDDQ_DDR), U1.P12 (VDDCORE), U1.P14 (VDDQ_DDR), U1.R13 (VDDCORE), U1.R15 (VDDQ_DDR)
1V8_DETECT: C7.1, C70.1, U1.B12 (VDDA1V8_DSI), U1.V11 (VDDA1V8_REG)
3.3V_VDD: C19.1, C22.1, C25.1, C28.1, C31.1, C33.1, L3.1, U1.A12 (VDD_DSI), U1.G13 (VDD_PLL2), U1.J5 (VDD_PLL), U1.K6 (VDD), U1.L3 (VDD_ANA), U1.L5 (VDD), U1.L7 (VDD), U1.M6 (VDD), U1.M8 (VDD), U1.N1 (PDR_ON_CORE), U1.N2 (PDR_ON), U1.N5 (VDD), U1.N7 (VDD), U1.N9 (VDD), U1.P6 (VDD), U1.P8 (VDD), U1.P10 (VDD), U1.R7 (VDD), U1.R9 (VDD), U1.R11 (VDD)
3V3_USB: C17.1, C68.1, U1.W12 (VDD3V3_USBHS), U1.W15 (VDD3V3_USBFS)
GNDS: C7.2, C9.1, C12.1, C14.1, C17.2, C18.2, C19.2, C20.2, C21.2, C22.2, C23.2, C24.2, C25.2, C26.2, C27.2, C28.2, C29.2, C30.2, C31.2, C32.2, C33.2, C34.2, C35.2, C38.1, C68.2, J12.2, U1.A1 (VSS), U1.A19 (VSS), U1.B2 (VSS), U1.B6 (VSS), U1.C3 (VSS), U1.C17 (VSS), U1.D1 (VSS), U1.D4 (VSS), U1.D5 (VSS), U1.D8 (VSS), U1.E2 (VSS), U1.E4 (VSS), U1.E5 (VSS), U1.E6 (VSS), U1.E8 (VSS), U1.E10 (VSS), U1.E12 (VSS), U1.E14 (VSS), U1.E16 (VSS), U1.F5 (VSS), U1.F7 (VSS), U1.F9 (VSS), U1.F11 (VSS), U1.F13 (VSS_PLL2), U1.F15 (VSS), U1.G2 (VSS), U1.G4 (VSS), U1.G6 (VSS), U1.G8 (VSS), U1.G10 (VSS), U1.G12 (VSS), U1.G14 (VSS), U1.H5 (VSS), U1.H7 (VSS), U1.H9 (VSS), U1.H11 (VSS), U1.H13 (VSS), U1.H15 (VSS), U1.J3 (VSS), U1.J4 (VSS_PLL), U1.J6 (VSS), U1.J8 (VSS), U1.J10 (VSS), U1.J12 (VSS), U1.J14 (VSS), U1.K2 (VSS), U1.K5 (VSS), U1.K7 (VSS), U1.K9 (VSS), U1.K11 (VSS), U1.K13 (VSS), U1.K15 (VSS), U1.L4 (VSS_ANA), U1.L6 (VSS), U1.L8 (VSS), U1.L10 (VSS), U1.L12 (VSS), U1.L14 (VSS), U1.M3 (VREF-), U1.M5 (VSS), U1.M7 (VSS), U1.M9 (VSS), U1.M11 (VSS), U1.M13 (VSS), U1.M15 (VSS), U1.N4 (VSSA), U1.N6 (VSS), U1.N8 (VSS), U1.N10 (VSS), U1.N12 (VSS), U1.N14 (VSS), U1.P5 (VSSA), U1.P7 (VSS), U1.P9 (VSS), U1.P11 (VSS), U1.P13 (VSS), U1.P15 (VSS), U1.R2 (VSS), U1.R5 (VSSA), U1.R6 (VSS), U1.R8 (VSS), U1.R10 (VSS), U1.R12 (VSS), U1.R14 (VSS), U1.R16 (VSS), U1.T4 (VSS), U1.T15 (BYPASS__REG1V8), U1.U3 (VSS), U1.U6 (VSS), U1.U8 (VSS), U1.U13 (VSS_USBHS), U1.U14 (VSS_USBHS), U1.U17 (VSS), U1.V12 (VSS_USBHS), U1.V15 (VSS_USBHS), U1.W1 (VSS), U1.W19 (VSS)
MPU_PWR_ON: TP1.1, U1.L1 (PWR_ON)
unnamed: C9.2, U1.W11 (VDDA1V1_REG)
unnamed: C12.2, L3.2, R25.1, U1.M4 (VDDA)
unnamed: C14.2, R25.2, U1.N3 (VREF+)
unnamed: C69.1, C70.2, U1.C12 (VSS_DSI), U1.C13 (VSS_DSI), U1.C14 (VSS_DSI), U1.C15 (VSS_DSI), U1.C16 (VSS_DSI)
unnamed: C69.2, U1.A16 (VDD1V2_DSI_PHY), U1.B16 (VDD1V2_DSI_REG)
unnamed: TP2.1, U1.P1 (PWR_LP)
VBAT: C38.2, J12.1, U1.H3 (VBAT)

Notes on the sheet:
DNF
