cracked-machine/STM32MP1_TestBoard_RevB/STM32MP1_TestBoard_RevB/USB_Conn.sch

## KiCad design STM32MP1_TestBoard_RevB/USB_Conn.sch (2021-04-06)

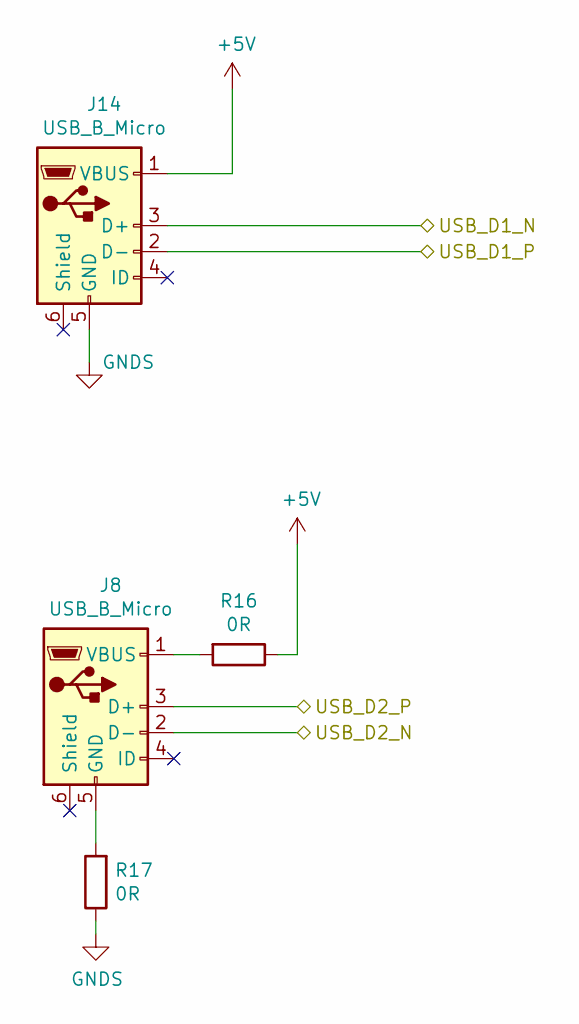
[picture p30: schematic USB_Conn.sch]

Parts:
J8, J13: USB_B_Micro; USB_Micro-B_Molex-105017-0001
R16, R17: 0R; R_0402_1005Metric_Pad0.72x0.64mm_HandSolder; LCSC C25087

Connections:
+5V: J13.1 (VBUS), R16.1
GNDS: J13.5 (GND), R17.1
unnamed: J8.1 (VBUS), R16.2
unnamed: J8.5 (GND), R17.2
USB_D1_N: J13.3 (D+)
USB_D1_P: J13.2 (D-)
USB_D2_N: J8.2 (D-)
USB_D2_P: J8.3 (D+)
